designer2k2/2d-xmas-tree/img/batteryweb.jpg

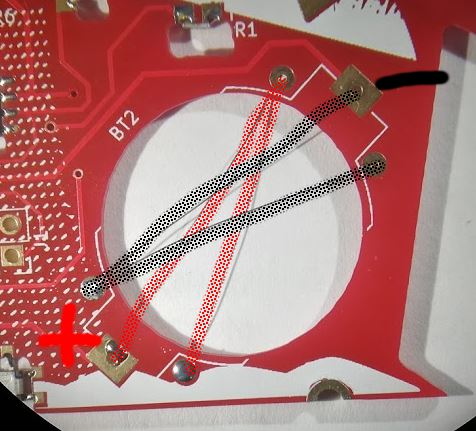
img/batteryweb.jpg
