designer2k2/2d-xmas-tree/img/led_orientation.PNG

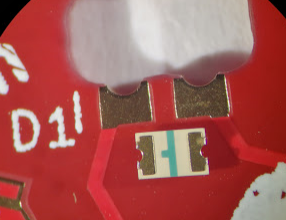
img/led_orientation.PNG
