designer2k2/2d-xmas-tree/pcb-kicad/inkscape/CopperExposed_01_back.png

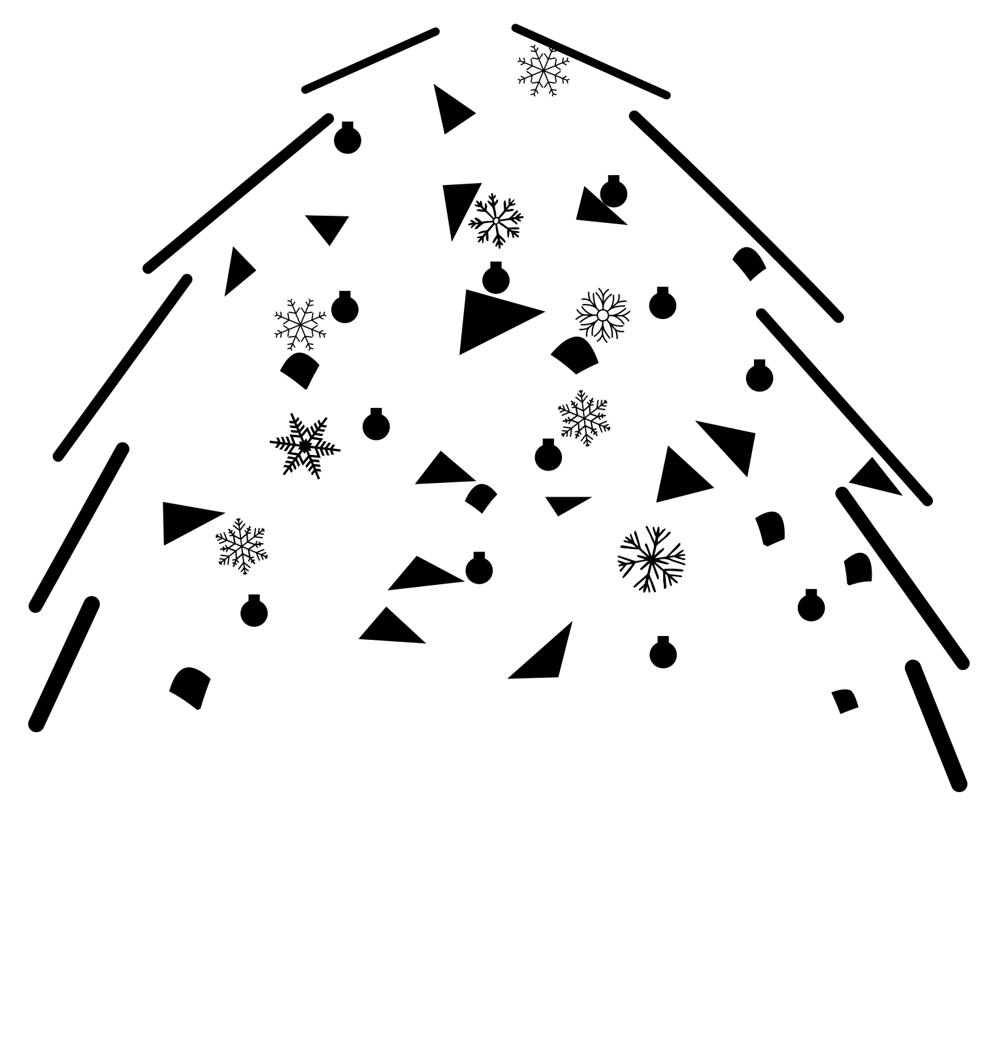
pcb-kicad/inkscape/CopperExposed_01_back.png
