designer2k2/2d-xmas-tree/pcb-kicad/inkscape/Snow_02.png

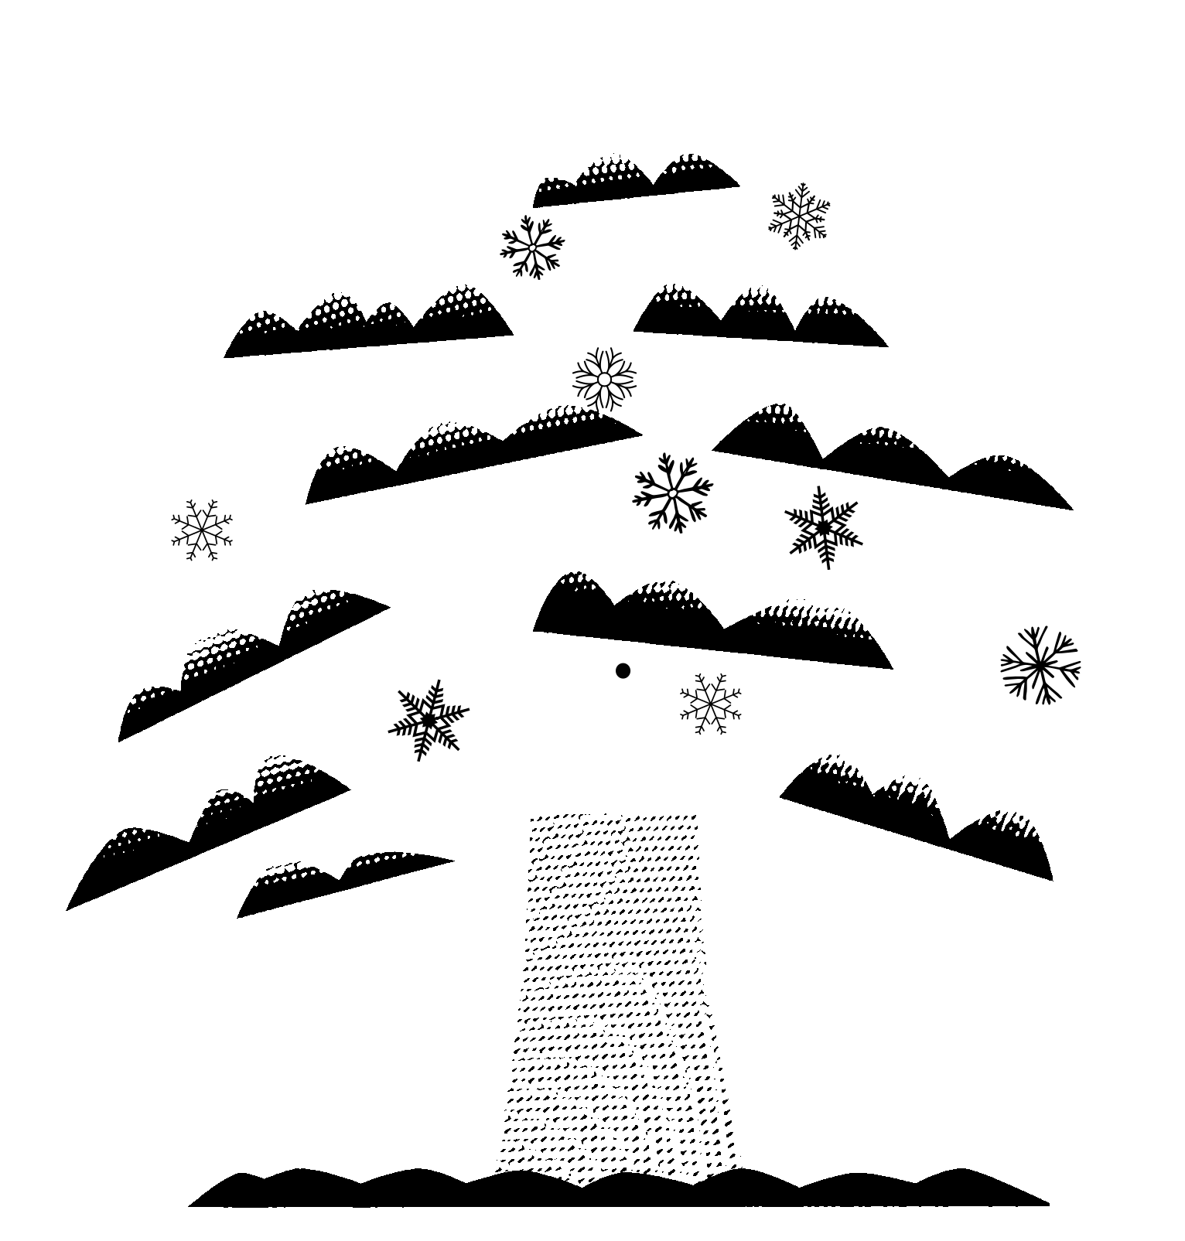
pcb-kicad/inkscape/Snow_02.png
