designer2k2/2d-xmas-tree/pcb-kicad/inkscape/Snow_02_back.png

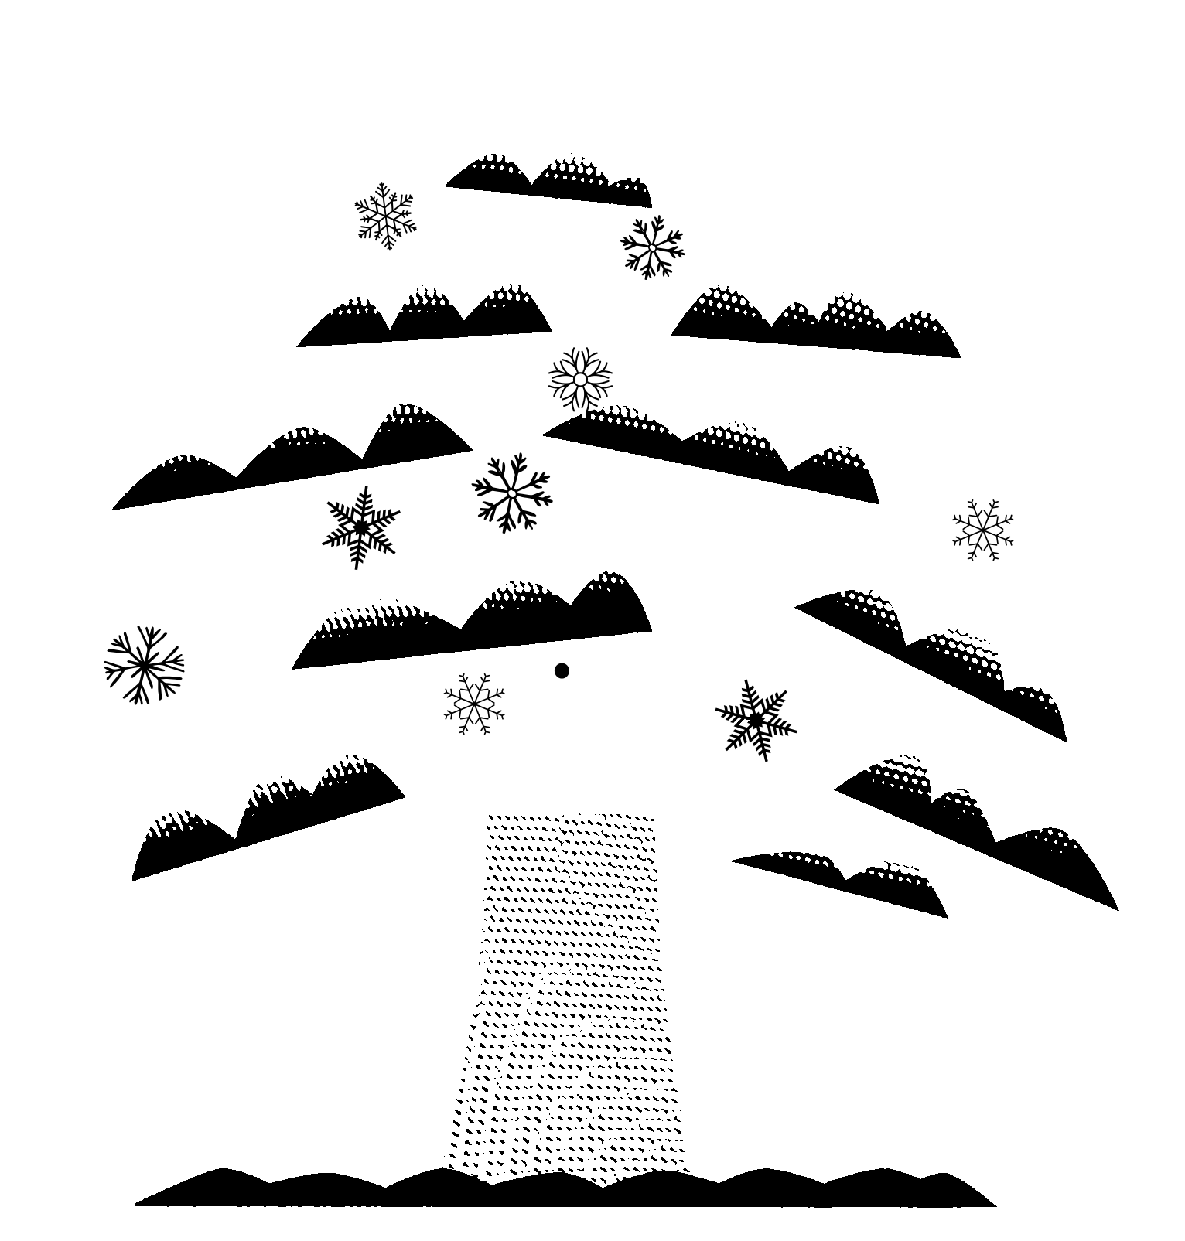
pcb-kicad/inkscape/Snow_02_back.png
