designer2k2/2d-xmas-tree/img/2d_xmas_tree_assembled.PNG

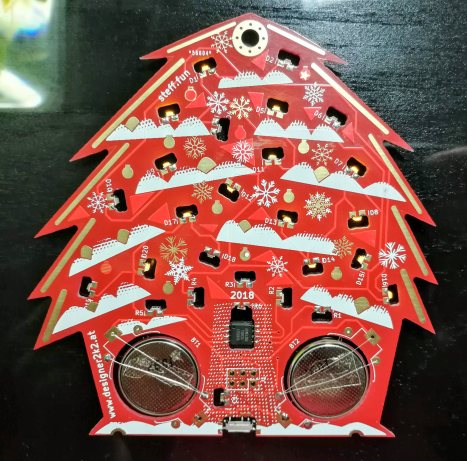
img/2d_xmas_tree_assembled.PNG
