designer2k2/2d-xmas-tree/img/attiny_soldered.JPG

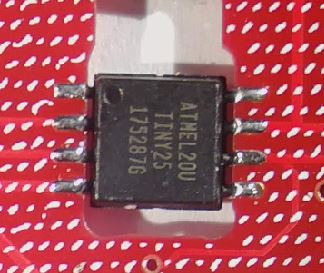
img/attiny_soldered.JPG
