designer2k2/2d-xmas-tree/pcb-kicad/inkscape/SolderMask_01.png

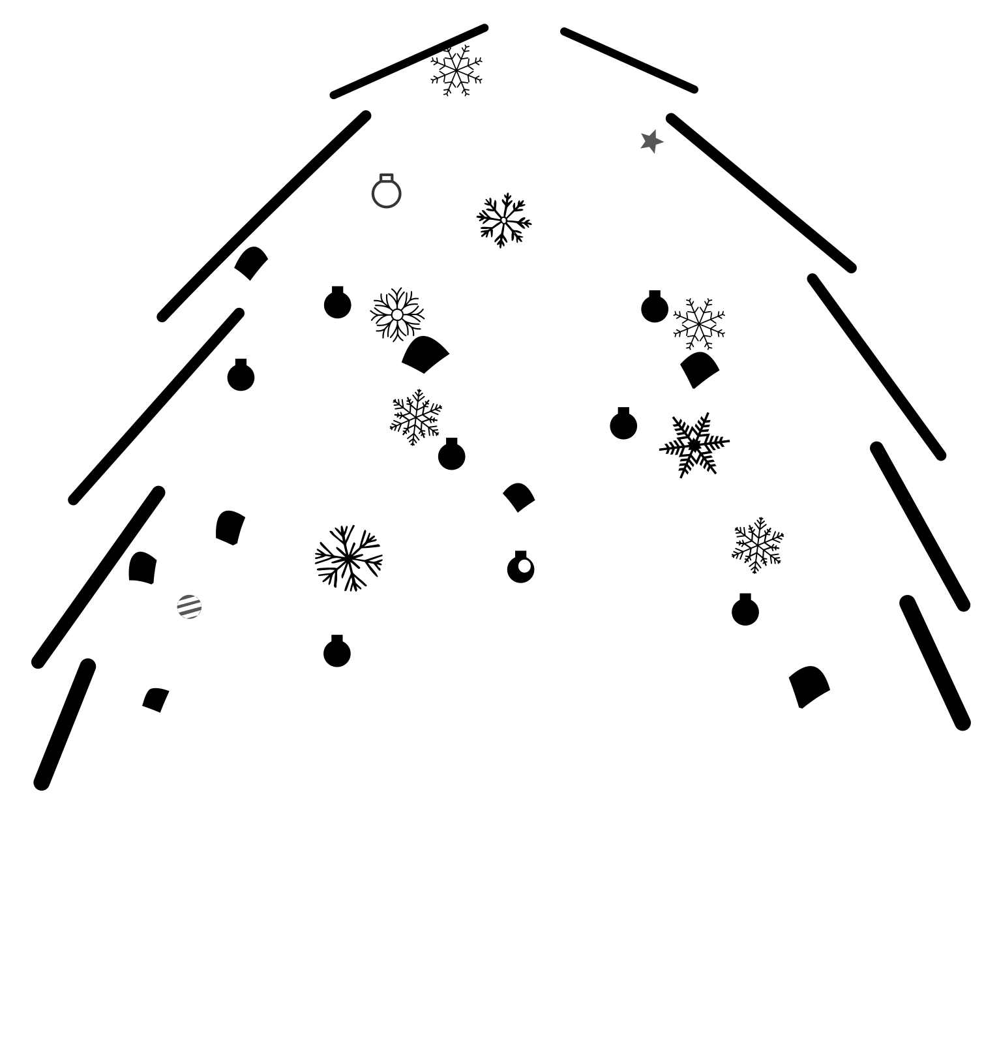
pcb-kicad/inkscape/SolderMask_01.png
