designer2k2/2d-xmas-tree/pcb-kicad/inkscape/SolderMask_01_back.png

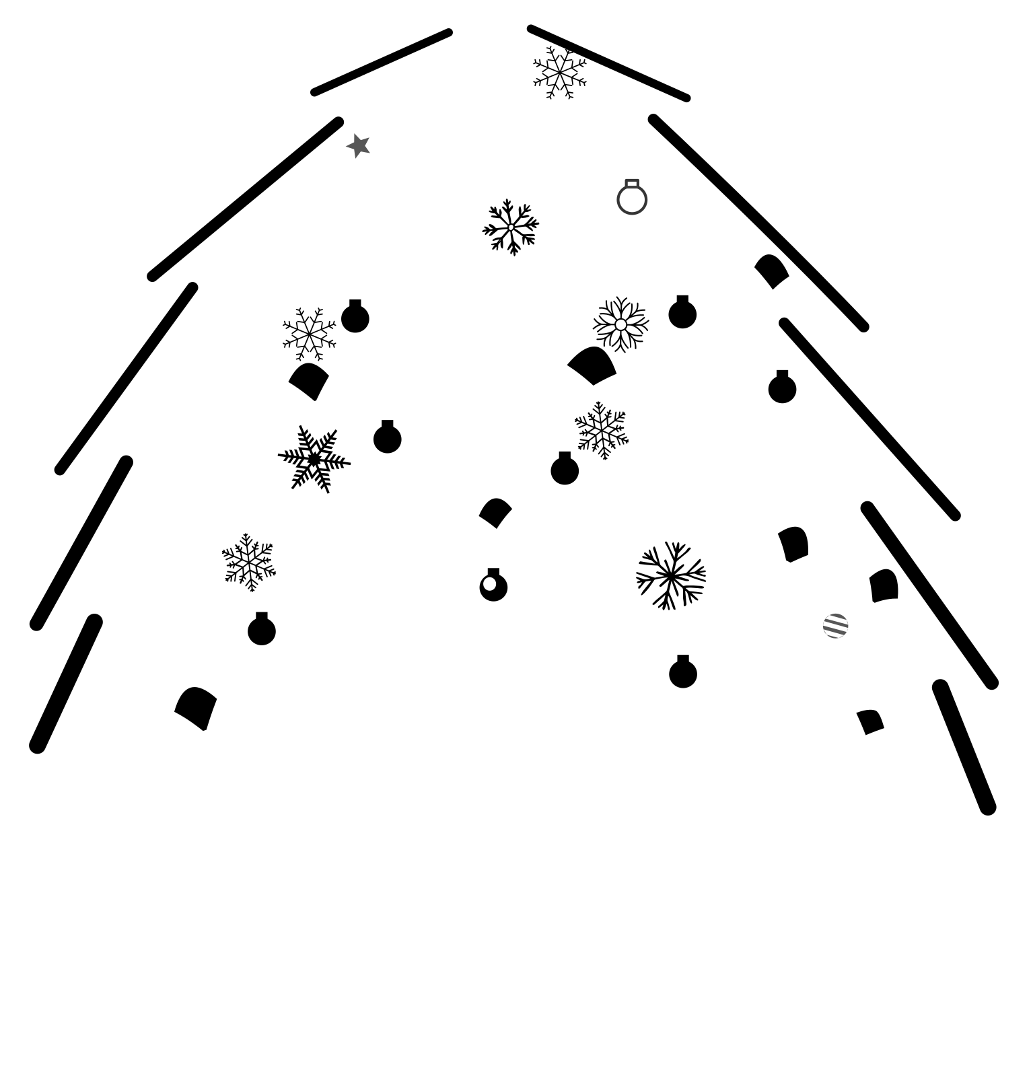
pcb-kicad/inkscape/SolderMask_01_back.png
